joeferner/telepresenceRobot/firmware/ring_buffer.c

#include "ring_buffer.h"
#include "util.h"

void ring_buffer_init(ring_buffer* ring, uint8_t* storage, uint16_t size) {
  ring->storage = storage;
  ring->size = size;
  ring->end = ring->storage + ring->size;
  ring->read = ring->storage;
  ring->write = ring->storage;
  ring->available = 0;
}

uint8_t ring_buffer_read_byte(ring_buffer* ring) {
  if(ring->available == 0) {
    return 0;
  }
  uint8_t ret = *ring->read++;
  ring->available--;
  if(ring->read >= ring->end) {
    ring->read = ring->storage;
  }
  return ret;
}

void ring_buffer_read(ring_buffer* ring, uint8_t* buffer, uint16_t size) {
  uint16_t i;
  
  // TODO can be optimized
  for(i = 0; i < size; i++) {
    buffer[i] = ring_buffer_read_byte(ring);
  }
}

void ring_buffer_write_byte(ring_buffer* ring, uint8_t b) {
  if(ring->available == ring->size) {
    return;
  }
  *ring->write = b;
  ring->write++;
  ring->available++;
  if(ring->write >= ring->end) {
    ring->write = ring->storage;
  }
}

void ring_buffer_write(ring_buffer* ring, const uint8_t* buffer, uint16_t size) {
  uint16_t i;
  
  // TODO can be optimized
  for(i = 0; i < size; i++) {
    ring_buffer_write_byte(ring, buffer[i]);
  }
}

uint16_t ring_buffer_readline(ring_buffer* ring, char* buffer, uint16_t size) {
  uint8_t b;
  uint16_t i;
  for(i = 0; i < min(ring->available, size - 1); i++) {
    b = ring_buffer_peekn(ring, i);
    if(b == '\n') {
      i++;
      ring_buffer_read(ring, (uint8_t*)buffer, i);
      buffer[i] = '\0';
      return i;
    }
  }
  buffer[0] = '\0';
  return 0;
}

uint8_t ring_buffer_peekn(ring_buffer* ring, uint16_t i) {
  if(i >= ring->available) {
    return 0;
  }
  
  uint8_t* p = ring->read + i;
  if(p >= ring->end) {
    p -= ring->size;
  }
  return *p;
}
