joeferner/telepresenceRobot/firmware/hw_config.h

#ifndef __HW_CONFIG_H
#define __HW_CONFIG_H

#include "platform_config.h"
#include "usb_type.h"
#include <stdio.h>

#define USART_RX_DATA_SIZE   2048

void Enter_LowPowerMode(void);
void Leave_LowPowerMode(void);
void USB_Cable_Config (FunctionalState NewState);
void Get_SerialNum(void);

#endif  /*__HW_CONFIG_H*/
